tangible-idea/ESP-with-3dprinter/hardwares/c3-supermini.png

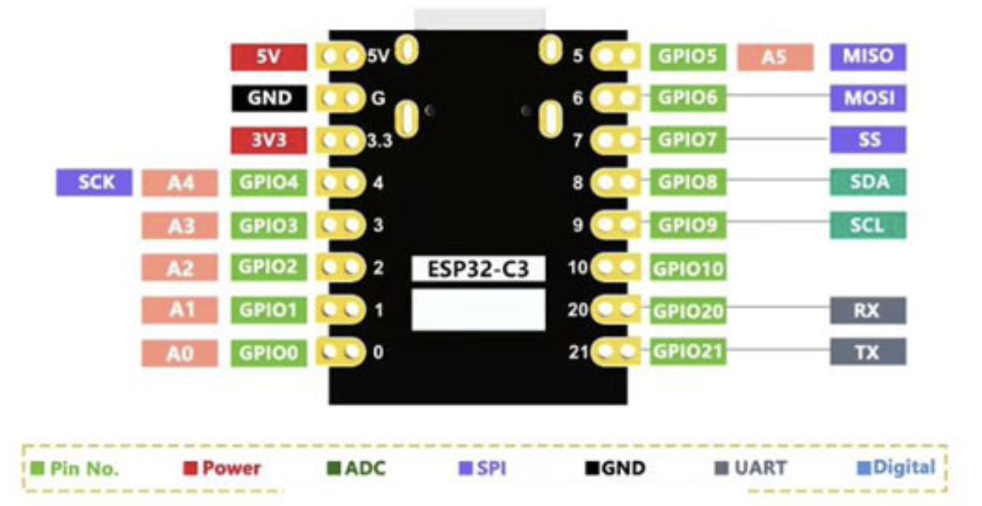
hardwares/c3-supermini.png
