tangible-idea/ESP-with-3dprinter/hardwares/picture_top.jpeg

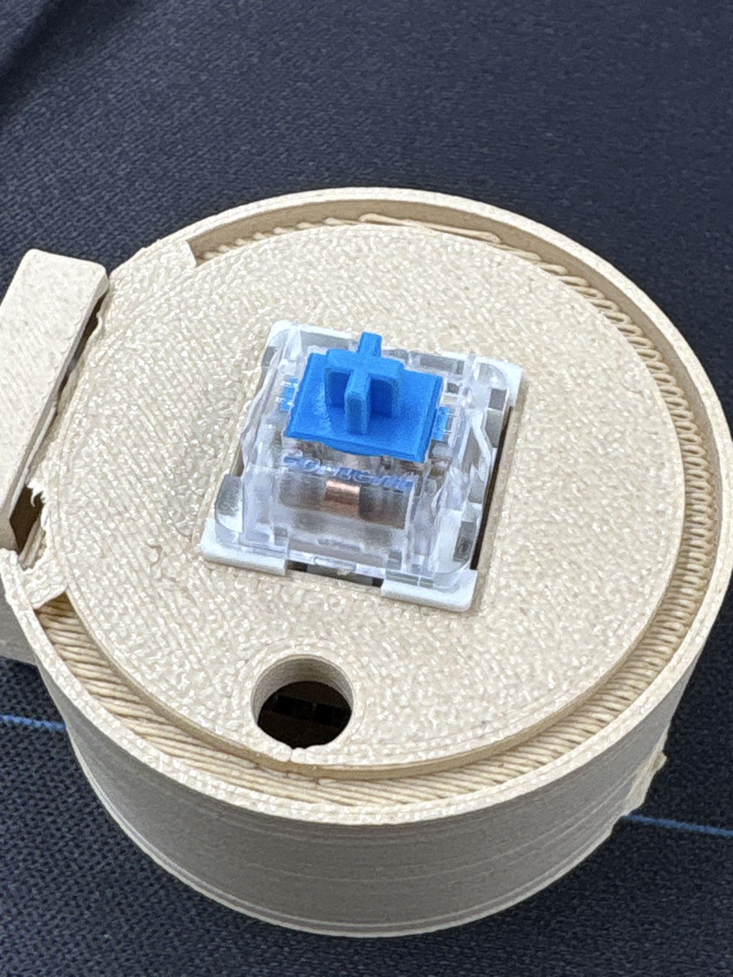
hardwares/picture_top.jpeg
