tangible-idea/ESP-with-3dprinter/hardwares/TP4056.png

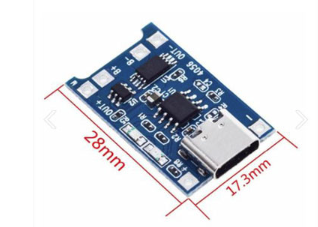
hardwares/TP4056.png
