tangible-idea/ESP-with-3dprinter/my_designs/promotions/IMG_5302.PNG

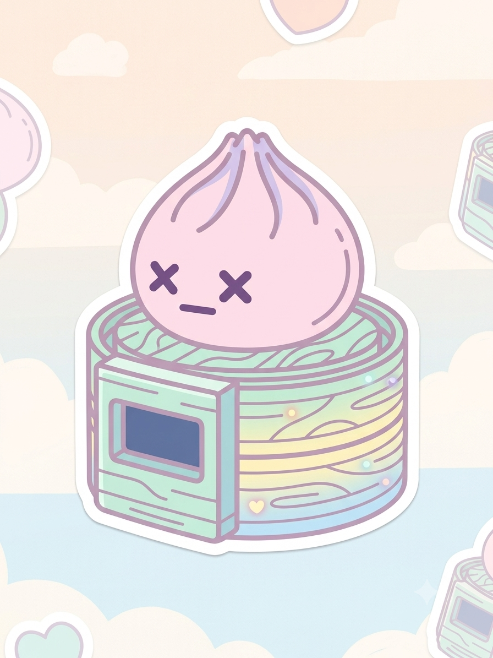
my_designs/promotions/IMG_5302.PNG
