tangible-idea/ESP-with-3dprinter/Screenshot 2026-07-04 at 1.25.15 pm.png

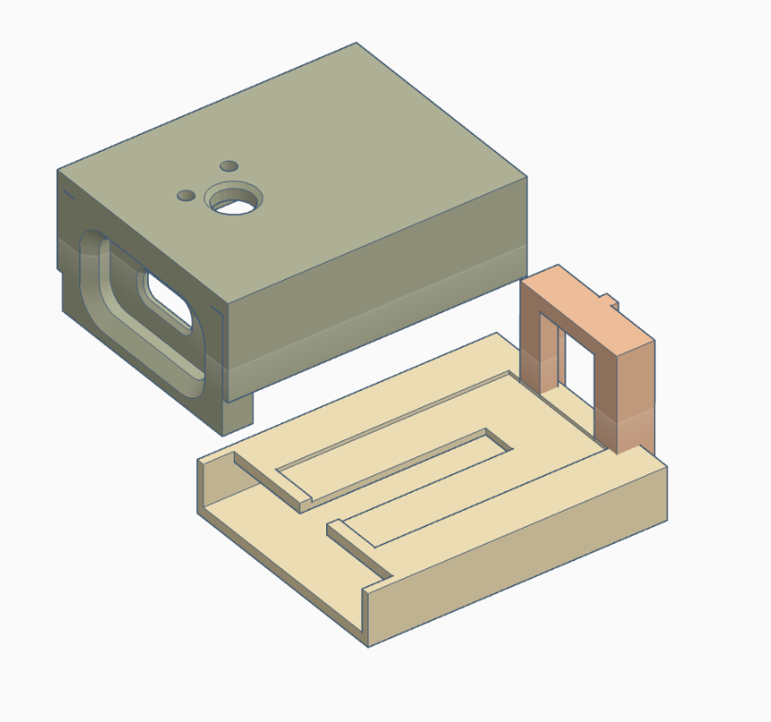
Screenshot 2026-07-04 at 1.25.15 pm.png
