tangible-idea/ESP-with-3dprinter/Screenshot 2026-07-04 at 2.11.48 pm.png

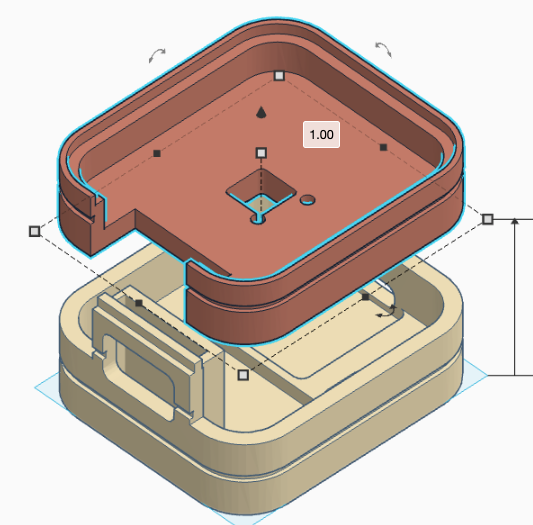
Screenshot 2026-07-04 at 2.11.48 pm.png
