tangible-idea/ESP-with-3dprinter/my_designs/2nd_floor_esp32_base.stl

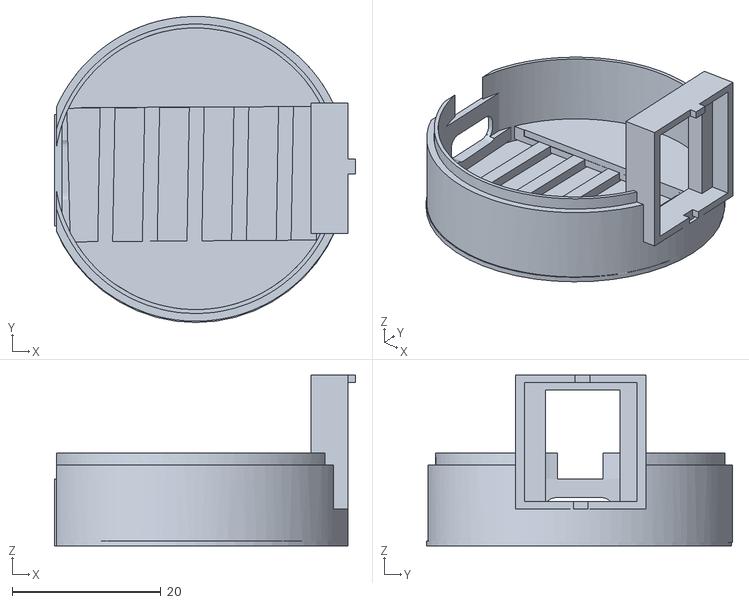
[picture p31: CAD file, 2026-07-04]
my_designs/2nd_floor_esp32_base.stl
40.5 x 41.2 x 23.0
