tangible-idea/ESP-with-3dprinter/stl_files/keyboard_switch_stand.stl

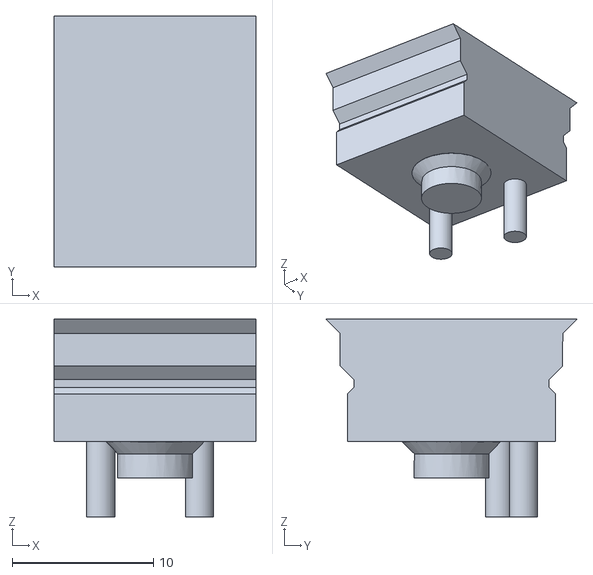
[picture p32: CAD file, 2026-07-04]
stl_files/keyboard_switch_stand.stl
14.3 x 17.8 x 14.0
