tangible-idea/ESP-with-3dprinter/web/dist/assets/usb_c_hole-Bh-LhuL4.stl

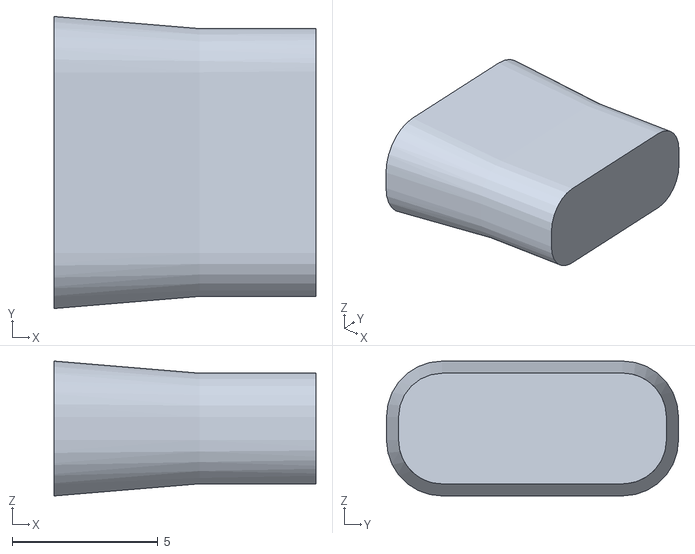
[picture p33: CAD file, 2026-07-04]
web/dist/assets/usb_c_hole-Bh-LhuL4.stl
9.00 x 10.0 x 4.64
