tangible-idea/ESP-with-3dprinter/stl_files/oled_0.49inch.stl

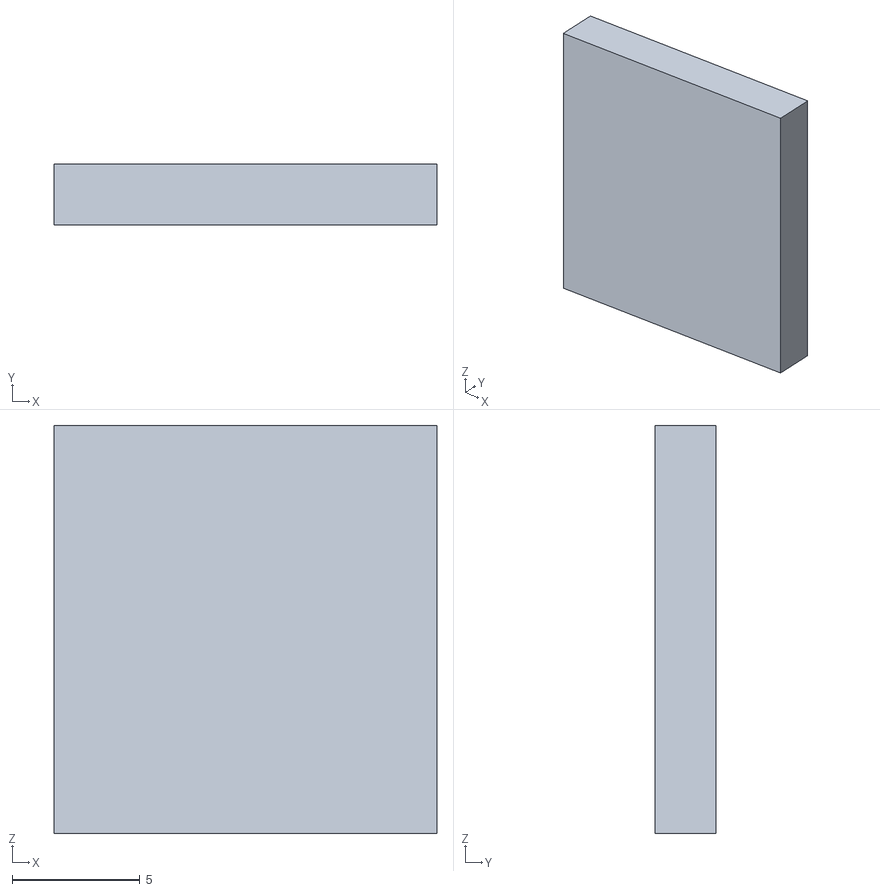
[picture p34: CAD file, 2026-07-04]
stl_files/oled_0.49inch.stl
15.0 x 2.40 x 16.0
