tangible-idea/ESP-with-3dprinter/web/dist/assets/esp32_c3_supermini-DsPQz_9p.stl

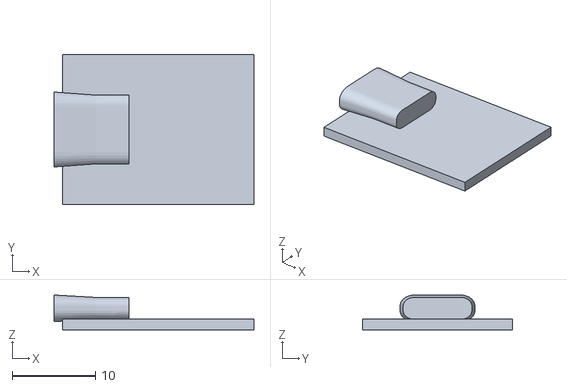
[picture p35: CAD file, 2026-07-04]
web/dist/assets/esp32_c3_supermini-DsPQz_9p.stl
24.0 x 18.0 x 4.20
