tangible-idea/ESP-with-3dprinter/stl_files/520Mah_battery.stl

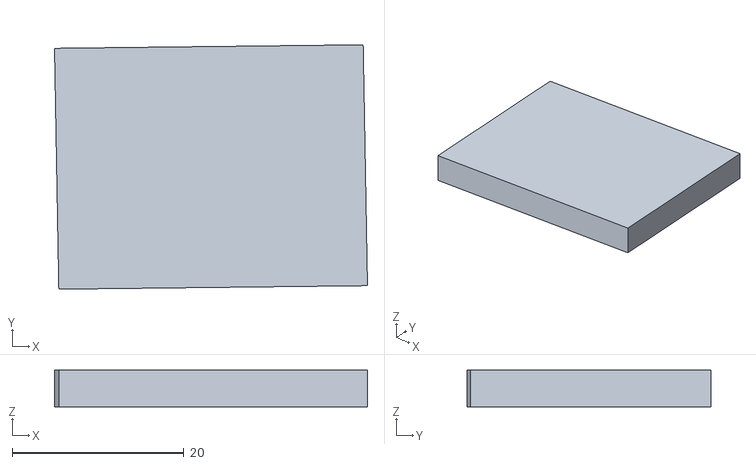
[picture p36: CAD file, 2026-07-04]
stl_files/520Mah_battery.stl
36.5 x 28.5 x 4.30
