tangible-idea/ESP-with-3dprinter/web/dist/assets/battery_charging_module-BhVwN-nm.stl

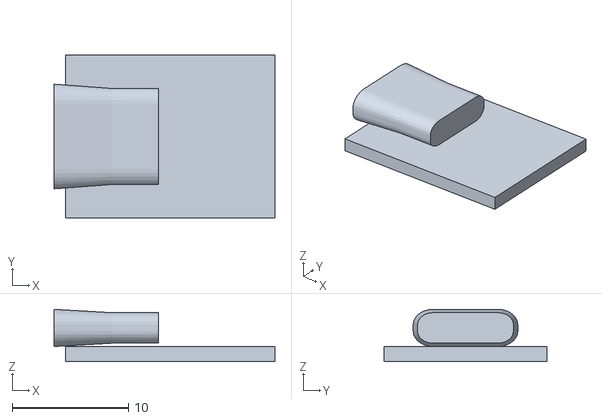
[picture p37: CAD file, 2026-07-04]
web/dist/assets/battery_charging_module-BhVwN-nm.stl
19.0 x 14.0 x 4.50
