tangible-idea/ESP-with-3dprinter/web/dist/assets/obj_2_sup 2.0 face-BjSeTE-s.stl

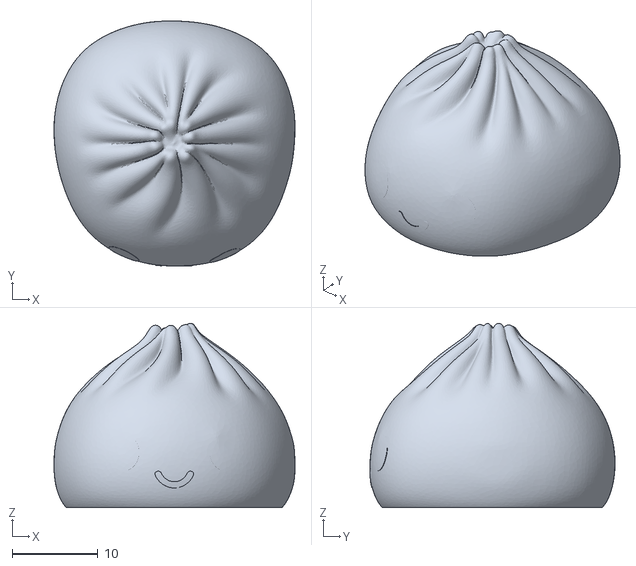
[picture p38: CAD file, 2026-07-04]
web/dist/assets/obj_2_sup 2.0 face-BjSeTE-s.stl
28.2 x 28.7 x 21.6
