tangible-idea/ESP-with-3dprinter/my_designs/todo_supporter_preview_2.png

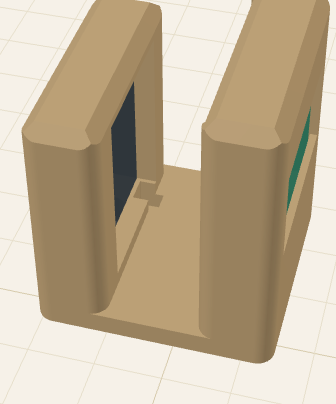
my_designs/todo_supporter_preview_2.png
